KiserDesigns/Monorail/Plate DXFs/Cutouts Only/m0n0rail_steam.dxf

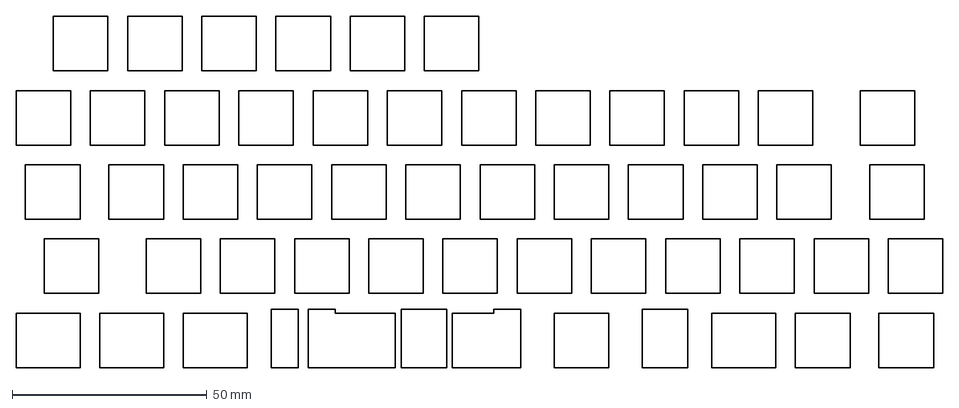
[picture p15: CAD file, 2022-03-02]
Plate DXFs/Cutouts Only/m0n0rail_steam.dxf
237.8 x 90.2 mm
