KiserDesigns/Monorail/Plate DXFs/Jet Hullagon.dxf

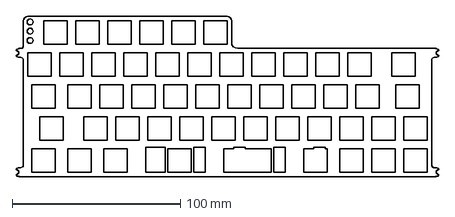
[picture p16: CAD file, 2022-03-02]
Plate DXFs/Jet Hullagon.dxf
251.3 x 95.2 mm
