KiserDesigns/Monorail/Plate DXFs/Cutouts Only/monorail_steam.dxf

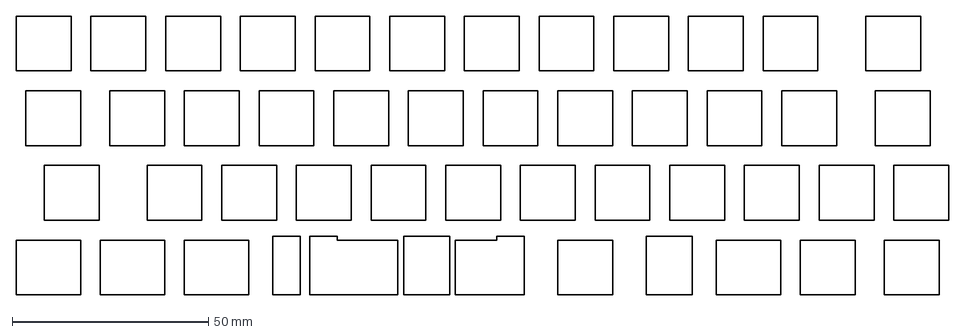
[picture p17: CAD file, 2022-03-02]
Plate DXFs/Cutouts Only/monorail_steam.dxf
237.8 x 71.1 mm
