KiserDesigns/Monorail/Plate DXFs/Diesel Vanagon.dxf

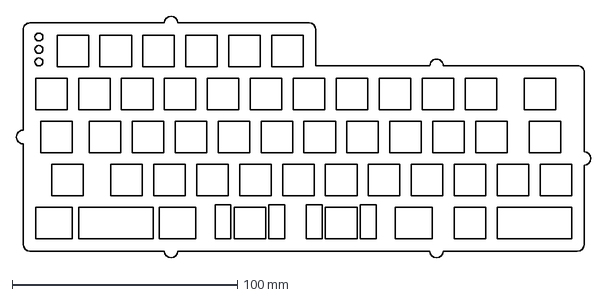
[picture p18: CAD file, 2022-03-02]
Plate DXFs/Diesel Vanagon.dxf
255.0 x 107.3 mm
