KiserDesigns/Monorail/Plate DXFs/Jet Coriander.dxf

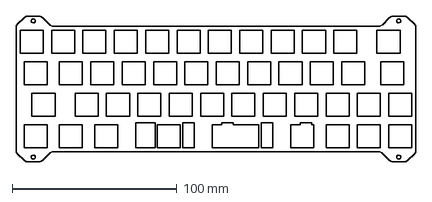
[picture p19: CAD file, 2022-03-02]
Plate DXFs/Jet Coriander.dxf
242.9 x 88.2 mm
