KiserDesigns/Monorail/Plate DXFs/Jet Tray Mount.dxf

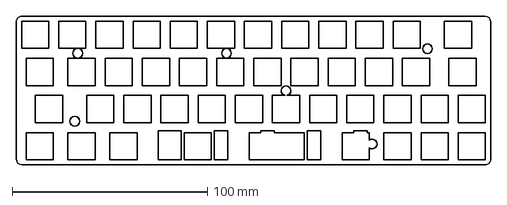
[picture p20: CAD file, 2022-03-02]
Plate DXFs/Jet Tray Mount.dxf
243.4 x 76.2 mm
