KiserDesigns/Monorail/Plate DXFs/Diesel Hull.dxf

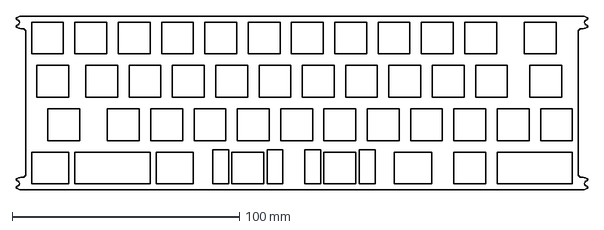
[picture p21: CAD file, 2022-03-02]
Plate DXFs/Diesel Hull.dxf
251.3 x 76.2 mm
