KiserDesigns/Monorail/Plate DXFs/Steam Coriander.dxf

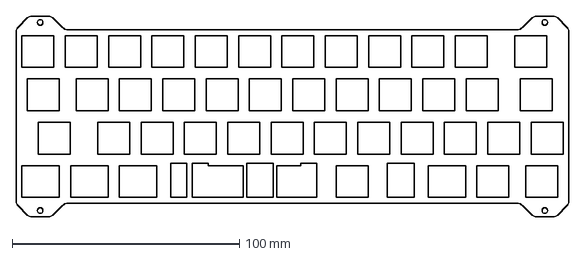
[picture p22: CAD file, 2022-03-02]
Plate DXFs/Steam Coriander.dxf
242.9 x 88.2 mm
