KiserDesigns/Monorail/Plate DXFs/Jet Hull.dxf

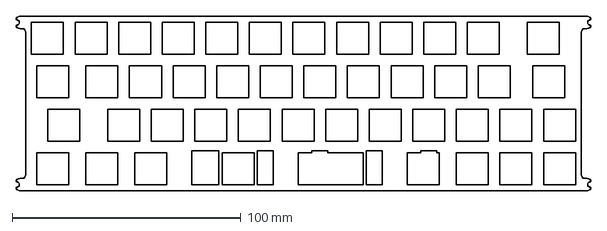
[picture p23: CAD file, 2022-03-02]
Plate DXFs/Jet Hull.dxf
251.3 x 76.2 mm
