KiserDesigns/Monorail/Plate DXFs/Combined Vanagon.dxf

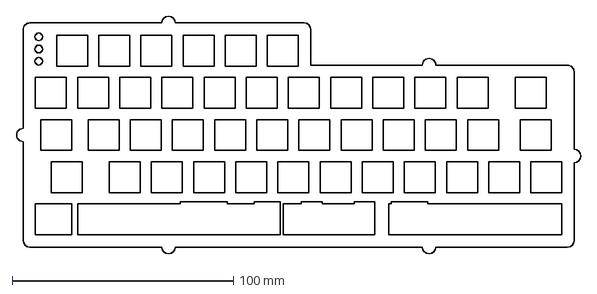
[picture p24: CAD file, 2022-03-02]
Plate DXFs/Combined Vanagon.dxf
255.0 x 107.3 mm
