KiserDesigns/Monorail/Plate DXFs/Steam Vanagon.dxf

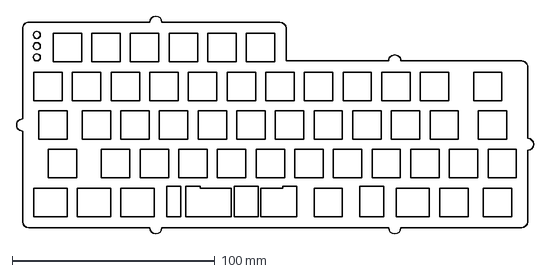
[picture p25: CAD file, 2022-03-02]
Plate DXFs/Steam Vanagon.dxf
255.0 x 107.3 mm
