KiserDesigns/Monorail/Plate DXFs/Combined Hullagon.dxf

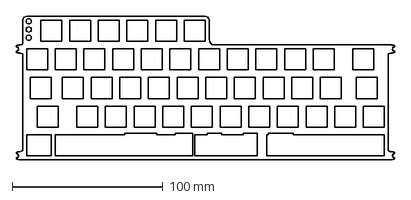
[picture p26: CAD file, 2022-03-02]
Plate DXFs/Combined Hullagon.dxf
251.3 x 95.2 mm
