KiserDesigns/Monorail/Plate DXFs/Combined Tray Mount.dxf

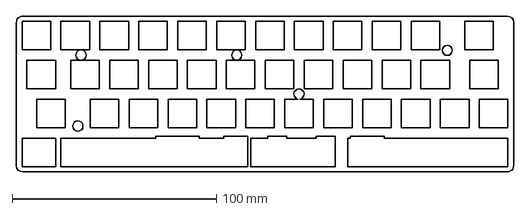
[picture p27: CAD file, 2022-03-02]
Plate DXFs/Combined Tray Mount.dxf
243.4 x 76.2 mm
