KiserDesigns/Monorail/Plate DXFs/Steam Hullagon.dxf

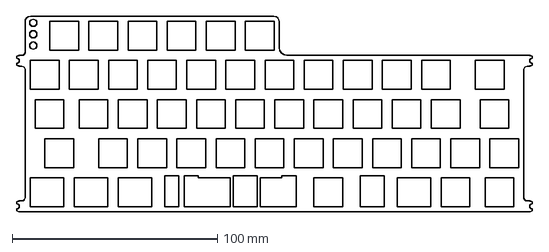
[picture p28: CAD file, 2022-03-02]
Plate DXFs/Steam Hullagon.dxf
251.3 x 95.2 mm
