KiserDesigns/Monorail/Plate DXFs/Steam Hull.dxf

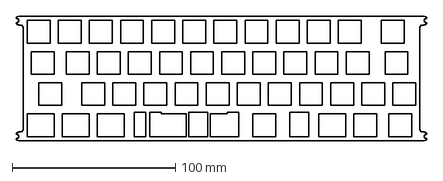
[picture p29: CAD file, 2022-03-02]
Plate DXFs/Steam Hull.dxf
251.3 x 76.2 mm
