KiserDesigns/Monorail/Plate DXFs/Steam Tray Mount.dxf

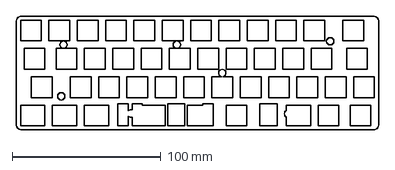
[picture p30: CAD file, 2022-03-02]
Plate DXFs/Steam Tray Mount.dxf
243.4 x 76.2 mm
