KiserDesigns/Monorail/PCB Sources/Monorail_Diesel_Reduced/Monorail_Diesel_Reduced.kicad_sch

## KiCad design PCB Sources/Monorail_Diesel_Reduced/Monorail_Diesel_Reduced.kicad_sch (2023-07-24)

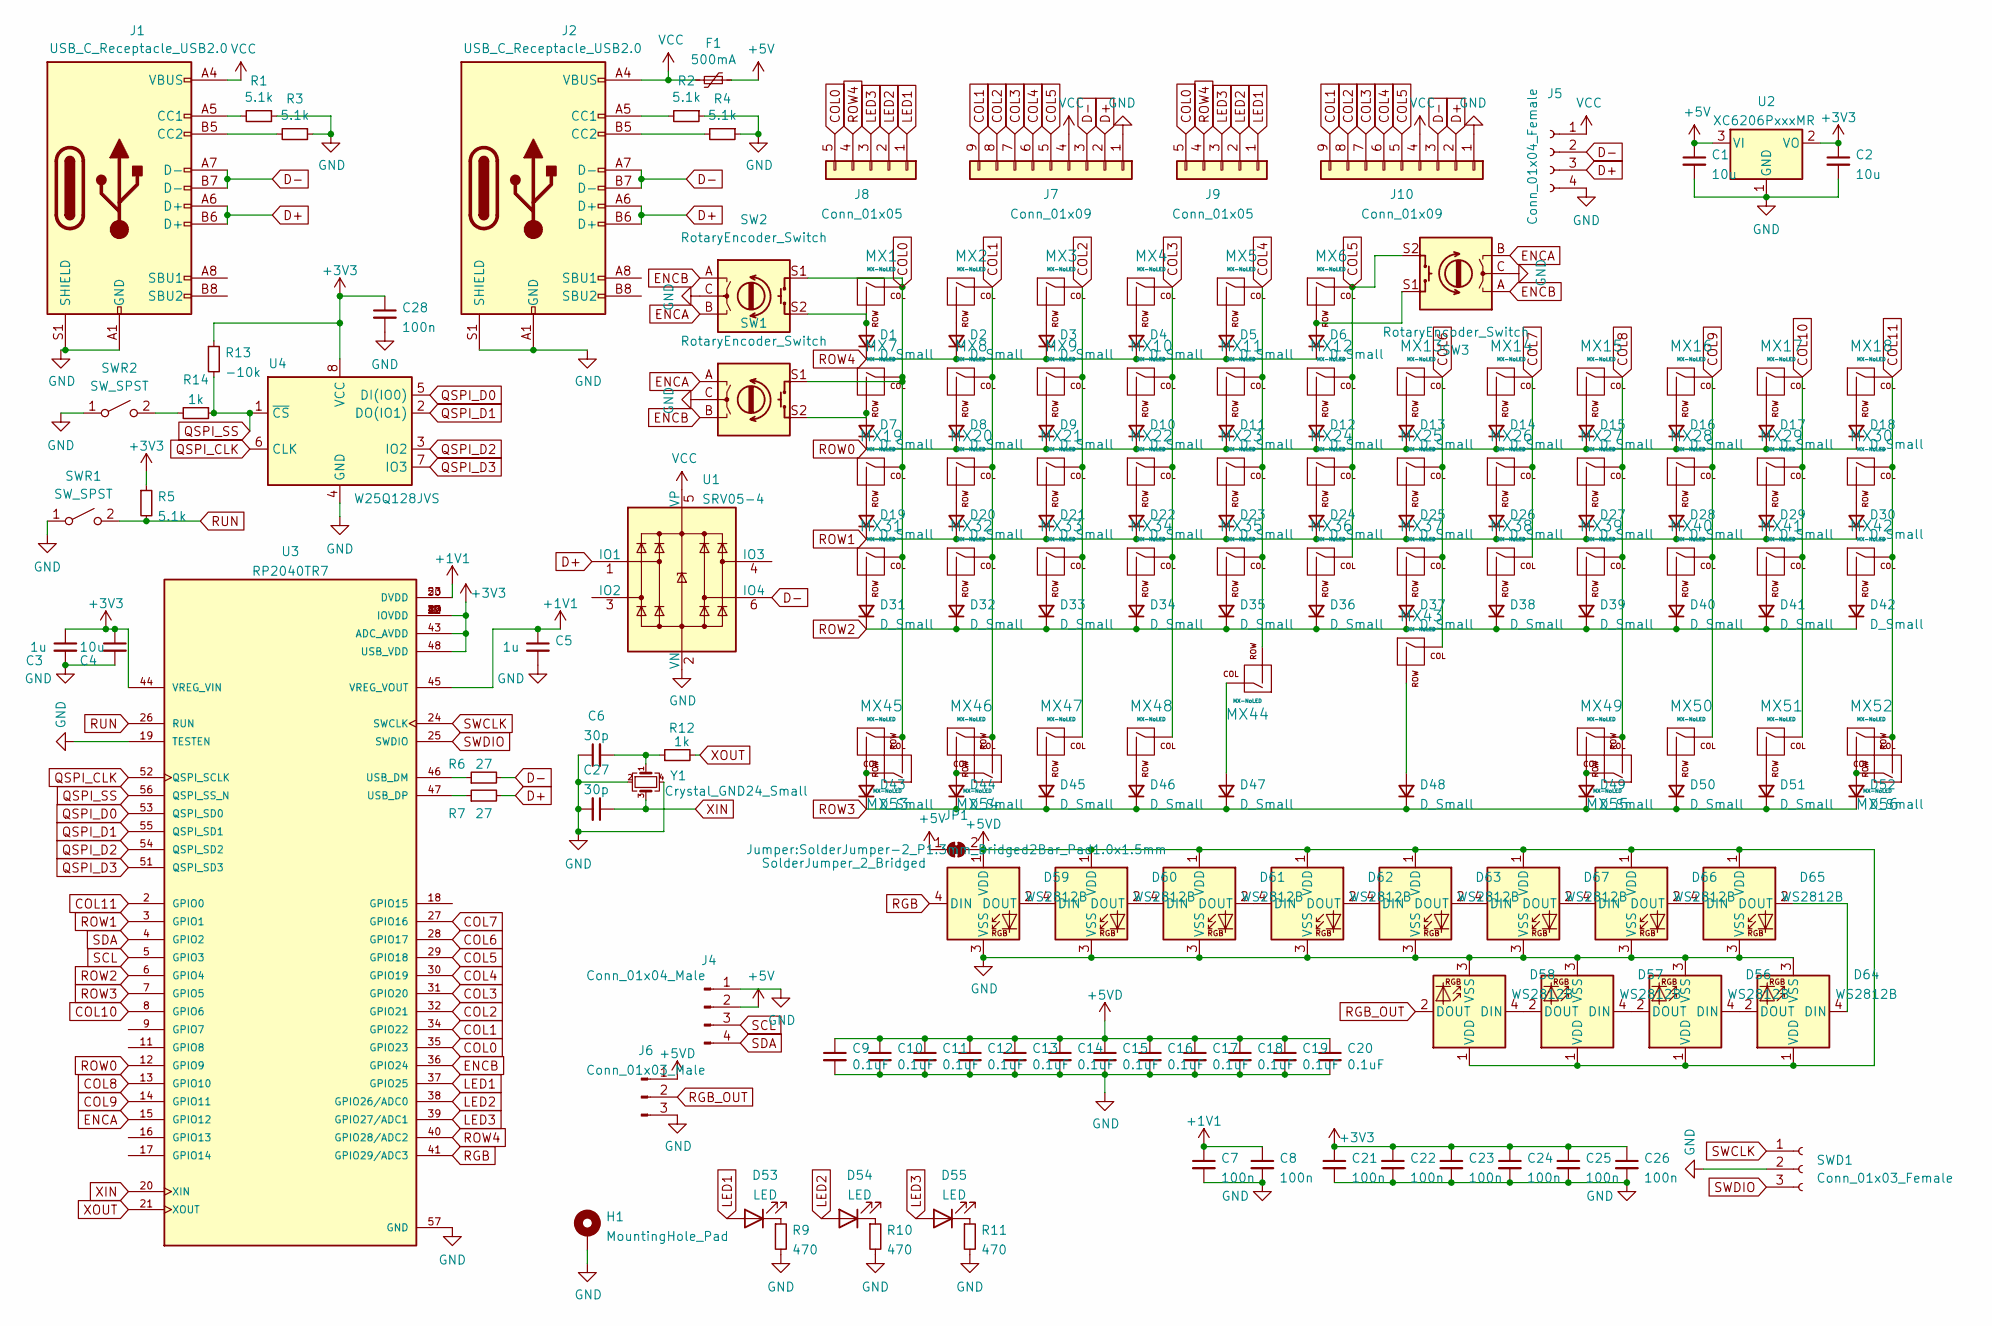
[picture p31: schematic Monorail_Diesel_Reduced.kicad_sch]

Parts:
C1, C2, C4: 10u; C_0402_1005Metric
C3, C5: 1u; C_0402_1005Metric
C6, C27: 30p; C_0402_1005Metric
C7, C8, C21, C22, C23, C24, C25, C26, C28: 100n; C_0402_1005Metric
C9, C10, C11, C12, C13, C14, C15, C16, C17, C18, C19, C20: 0.1uF; C_0603_1608Metric
D1, D2, D3, D4, D5, D6, D7, D8, D9, D10, D11, D12, D13, D14, D15, D16, D17, D18, D19, D20, D21, D22, D23, D24, D25, D26, D27, D28, D29, D30, D31, D32, D33, D34, D35, D36, D37, D38, D39, D40, D41, D42, D43, D44, D45, D46, D47, D48, D49, D50, D51, D52: D_Small; D_SOD-123
D53, D54, D55: LED; LED_D3.0mm
D56, D57, D58, D59, D60, D61, D62, D63, D64, D65, D66, D67: WS2812B; LED_WS2812B_2020
F1: 500mA; Fuse_1206_3216Metric
H1: MountingHole_Pad; Minivan-reference
J1, J2: USB_C_Receptacle_USB2.0; USB_C_Receptacle_HRO_TYPE-C-31-M-12
J4: Conn_01x04_Male; PinHeader_1x04_P2.54mm_Vertical
J5: Conn_01x04_Female; JST_SH_SM04B-SRSS-TB_1x04-1MP_P1.00mm_Horizontal
J6: Conn_01x03_Male; PinHeader_1x03_P2.54mm_Vertical
J7, J10: Conn_01x09; PinHeader_1x09_P2.54mm_Vertical
J8, J9: Conn_01x05; PinHeader_1x05_P2.54mm_Vertical
JP1: SolderJumper_2_Bridged; SolderJumper-2_P1.3mm_Bridged2Bar_Pad1.0x1.5mm
MX1, MX2, MX3, MX4, MX5, MX6, MX7, MX8, MX9, MX10, MX11, MX12, MX13, MX14, MX15, MX16, MX17, MX20, MX21, MX22, MX23, MX24, MX25, MX26, MX27, MX28, MX29, MX32, MX33, MX34, MX35, MX36, MX37, MX38, MX39, MX40, MX41, MX42, MX45, MX46, MX47, MX48, MX51, MX56: MX-NoLED; MXOnly-1U-Hotswap
MX18, MX31, MX52: MX-NoLED; MXOnly-1.75U-Hotswap
MX19, MX53, MX55: MX-NoLED; MXOnly-1.25U-Hotswap
MX30, MX49, MX50, MX54: MX-NoLED; MXOnly-1.5U-Hotswap
MX43: MX-NoLED; MXOnly-2U-Hotswap-ReversedStabilizers
MX44: MX-NoLED; MXOnly-2.25U-Hotswap-ReversedStabilizers
R1, R2, R3, R4: 5.1k; R_0603_1608Metric
R5: 5.1k; R_0402_1005Metric
R6, R7: 27; R_0402_1005Metric
R9, R10, R11: 470; R_0603_1608Metric
R12, R14: 1k; R_0402_1005Metric
R13: -10k; R_0603_1608Metric
SW1, SW2, SW3: RotaryEncoder_Switch; RotaryEncoder_Alps_EC11E-Switch_Vertical_H20mm
SWD1: Conn_01x03_Female; PinHeader_1x03_P2.54mm_Vertical
SWR1, SWR2: SW_SPST; SW_SPST_TL3342
U1: SRV05-4; SOT-23-6
U2: XC6206PxxxMR; SOT-23
U3: RP2040TR7; QFN40P700X700X90-57N; PARTREV 1.7.1
U4: W25Q128JVS; SOIC-8_5.23x5.23mm_P1.27mm
Y1: Crystal_GND24_Small; Crystal_SMD_3225-4Pin_3.2x2.5mm

Connections:
+1V1: C5.1, C7.1, C8.1, U3.23 (DVDD), U3.45 (VREG_VOUT), U3.50 (DVDD)
+3V3: C2.1, C3.1, C4.1, C21.1, C22.1, C23.1, C24.1, C25.1, C26.1, C28.1, R5.1, R13.1, U2.2 (VO), U3.1 (IOVDD), U3.10 (IOVDD), U3.22 (IOVDD), U3.33 (IOVDD), U3.42 (IOVDD), U3.43 (ADC_AVDD), U3.44 (VREG_VIN), U3.48 (USB_VDD), U3.49 (IOVDD), U4.8 (VCC)
+5V: C1.1, F1.1, J4.2, JP1.1 (A), U2.3 (VI)
+5VD: C9.1, C10.1, C11.1, C12.1, C13.1, C14.1, C15.1, C16.1, C17.1, C18.1, C19.1, C20.1, D56.1 (VDD), D57.1 (VDD), D58.1 (VDD), D59.1 (VDD), D60.1 (VDD), D61.1 (VDD), D62.1 (VDD), D63.1 (VDD), D64.1 (VDD), D65.1 (VDD), D66.1 (VDD), D67.1 (VDD), J6.1, JP1.2 (B)
COL0: J8.5, J9.5, MX1.1 (COL), MX7.1 (COL), MX19.1 (COL), MX31.1 (COL), MX45.1 (COL), MX53.2 (ROW), SW1.S1, SW2.S1, U3.35 (GPIO23)
COL1: J7.9, J10.9, MX2.1 (COL), MX8.1 (COL), MX20.1 (COL), MX32.1 (COL), MX46.1 (COL), MX54.2 (ROW), U3.34 (GPIO22)
COL2: J7.8, J10.8, MX3.1 (COL), MX9.1 (COL), MX21.1 (COL), MX33.1 (COL), MX47.1 (COL), U3.32 (GPIO21)
COL3: J7.7, J10.7, MX4.1 (COL), MX10.1 (COL), MX22.1 (COL), MX34.1 (COL), MX48.1 (COL), U3.31 (GPIO20)
COL4: J7.6, J10.6, MX5.1 (COL), MX11.1 (COL), MX23.1 (COL), MX35.1 (COL), MX44.2 (ROW), U3.30 (GPIO19)
COL5: J7.5, J10.5, MX6.1 (COL), MX12.1 (COL), MX24.1 (COL), MX36.1 (COL), SW3.S2, U3.29 (GPIO18)
COL6: MX13.1 (COL), MX25.1 (COL), MX37.1 (COL), MX43.1 (COL), U3.28 (GPIO17)
COL7: MX14.1 (COL), MX26.1 (COL), MX38.1 (COL), U3.27 (GPIO16)
COL8: MX15.1 (COL), MX27.1 (COL), MX39.1 (COL), MX49.1 (COL), MX55.2 (ROW), U3.13 (GPIO10)
COL9: MX16.1 (COL), MX28.1 (COL), MX40.1 (COL), MX50.1 (COL), U3.14 (GPIO11)
COL10: MX17.1 (COL), MX29.1 (COL), MX41.1 (COL), MX51.1 (COL), U3.8 (GPIO6)
COL11: MX18.1 (COL), MX30.1 (COL), MX42.1 (COL), MX52.1 (COL), MX56.2 (ROW), U3.2 (GPIO0)
D+: J1.A6 (D+), J1.B6 (D+), J2.A6 (D+), J2.B6 (D+), J5.3, J7.2, J10.2, R7.2, U1.1 (IO1)
D-: J1.A7 (D-), J1.B7 (D-), J2.A7 (D-), J2.B7 (D-), J5.2, J7.3, J10.3, R6.2, U1.6 (IO4)
ENCA: SW1.A, SW2.B, SW3.B, U3.15 (GPIO12)
ENCB: SW1.B, SW2.A, SW3.A, U3.36 (GPIO24)
GND: C1.2, C2.2, C3.2, C4.2, C5.2, C6.1, C7.2, C8.2, C9.2, C10.2, C11.2, C12.2, C13.2, C14.2, C15.2, C16.2, C17.2, C18.2, C19.2, C20.2, C21.2, C22.2, C23.2, C24.2, C25.2, C26.2, C27.2, C28.2, D56.3 (VSS), D57.3 (VSS), D58.3 (VSS), D59.3 (VSS), D60.3 (VSS), D61.3 (VSS), D62.3 (VSS), D63.3 (VSS), D64.3 (VSS), D65.3 (VSS), D66.3 (VSS), D67.3 (VSS), H1.1, J1.A1 (GND), J1.A12 (GND), J1.B1 (GND), J1.B12 (GND), J1.S1 (SHIELD), J2.A1 (GND), J2.A12 (GND), J2.B1 (GND), J2.B12 (GND), J2.S1 (SHIELD), J4.1, J5.4, J6.3, J7.1, J10.1, R1.1, R2.1, R3.1, R4.1, R9.2, R10.2, R11.2, SW1.C, SW2.C, SW3.C, SWD1.2, SWR1.1 (A), SWR2.1 (A), U1.2 (VN), U2.1 (GND), U3.19 (TESTEN), U3.57 (GND), U4.4 (GND), Y1.2, Y1.4
LED1: D53.2 (A), J8.1, J9.1, U3.37 (GPIO25)
LED2: D54.2 (A), J8.2, J9.2, U3.38 (GPIO26/ADC0)
LED3: D55.2 (A), J8.3, J9.3, U3.39 (GPIO27/ADC1)
unnamed: C6.2, R12.1, Y1.1
unnamed: D1.2 (A), MX1.2 (ROW), SW2.S2
unnamed: D2.2 (A), MX2.2 (ROW)
unnamed: D3.2 (A), MX3.2 (ROW)
unnamed: D4.2 (A), MX4.2 (ROW)
unnamed: D5.2 (A), MX5.2 (ROW)
unnamed: D6.2 (A), MX6.2 (ROW), SW3.S1
unnamed: D7.2 (A), MX7.2 (ROW), SW1.S2
unnamed: D8.2 (A), MX8.2 (ROW)
unnamed: D9.2 (A), MX9.2 (ROW)
unnamed: D10.2 (A), MX10.2 (ROW)
unnamed: D11.2 (A), MX11.2 (ROW)
unnamed: D12.2 (A), MX12.2 (ROW)
unnamed: D13.2 (A), MX13.2 (ROW)
unnamed: D14.2 (A), MX14.2 (ROW)
unnamed: D15.2 (A), MX15.2 (ROW)
unnamed: D16.2 (A), MX16.2 (ROW)
unnamed: D17.2 (A), MX17.2 (ROW)
unnamed: D18.2 (A), MX18.2 (ROW)
unnamed: D19.2 (A), MX19.2 (ROW)
unnamed: D20.2 (A), MX20.2 (ROW)
unnamed: D21.2 (A), MX21.2 (ROW)
unnamed: D22.2 (A), MX22.2 (ROW)
unnamed: D23.2 (A), MX23.2 (ROW)
unnamed: D24.2 (A), MX24.2 (ROW)
unnamed: D25.2 (A), MX25.2 (ROW)
unnamed: D26.2 (A), MX26.2 (ROW)
unnamed: D27.2 (A), MX27.2 (ROW)
unnamed: D28.2 (A), MX28.2 (ROW)
unnamed: D29.2 (A), MX29.2 (ROW)
unnamed: D30.2 (A), MX30.2 (ROW)
unnamed: D31.2 (A), MX31.2 (ROW)
unnamed: D32.2 (A), MX32.2 (ROW)
unnamed: D33.2 (A), MX33.2 (ROW)
unnamed: D34.2 (A), MX34.2 (ROW)
unnamed: D35.2 (A), MX35.2 (ROW)
unnamed: D36.2 (A), MX36.2 (ROW)
unnamed: D37.2 (A), MX37.2 (ROW)
unnamed: D38.2 (A), MX38.2 (ROW)
unnamed: D39.2 (A), MX39.2 (ROW)
unnamed: D40.2 (A), MX40.2 (ROW)
unnamed: D41.2 (A), MX41.2 (ROW)
unnamed: D42.2 (A), MX42.2 (ROW)
unnamed: D43.2 (A), MX45.2 (ROW), MX53.1 (COL)
unnamed: D44.2 (A), MX46.2 (ROW), MX54.1 (COL)
unnamed: D45.2 (A), MX47.2 (ROW)
unnamed: D46.2 (A), MX48.2 (ROW)
unnamed: D47.2 (A), MX44.1 (COL)
unnamed: D48.2 (A), MX43.2 (ROW)
unnamed: D49.2 (A), MX49.2 (ROW), MX55.1 (COL)
unnamed: D50.2 (A), MX50.2 (ROW)
unnamed: D51.2 (A), MX51.2 (ROW)
unnamed: D52.2 (A), MX52.2 (ROW), MX56.1 (COL)
unnamed: D53.1 (K), R9.1
unnamed: D54.1 (K), R10.1
unnamed: D55.1 (K), R11.1
unnamed: D56.2 (DOUT), D57.4 (DIN)
unnamed: D56.4 (DIN), D64.2 (DOUT)
unnamed: D57.2 (DOUT), D58.4 (DIN)
unnamed: D59.2 (DOUT), D60.4 (DIN)
unnamed: D60.2 (DOUT), D61.4 (DIN)
unnamed: D61.2 (DOUT), D62.4 (DIN)
unnamed: D62.2 (DOUT), D63.4 (DIN)
unnamed: D63.2 (DOUT), D67.4 (DIN)
unnamed: D64.4 (DIN), D65.2 (DOUT)
unnamed: D65.4 (DIN), D66.2 (DOUT)
unnamed: D66.4 (DIN), D67.2 (DOUT)
unnamed: J1.A5 (CC1), R1.2
unnamed: J1.B5 (CC2), R3.2
unnamed: J2.A5 (CC1), R2.2
unnamed: J2.B5 (CC2), R4.2
unnamed: R6.1, U3.46 (USB_DM)
unnamed: R7.1, U3.47 (USB_DP)
unnamed: R14.2, SWR2.2 (B)
QSPI_CLK: U3.52 (QSPI_SCLK), U4.6 (CLK)
QSPI_D0: U3.53 (QSPI_SD0), U4.5 (DI(IO0))
QSPI_D1: U3.55 (QSPI_SD1), U4.2 (DO(IO1))
QSPI_D2: U3.54 (QSPI_SD2), U4.3 (IO2)
QSPI_D3: U3.51 (QSPI_SD3), U4.7 (IO3)
QSPI_SS: R13.2, R14.1, U3.56 (QSPI_SS_N), U4.1 (~CS)
RGB: D59.4 (DIN), U3.41 (GPIO29/ADC3)
RGB_OUT: D58.2 (DOUT), J6.2
ROW0: D7.1 (K), D8.1 (K), D9.1 (K), D10.1 (K), D11.1 (K), D12.1 (K), D13.1 (K), D14.1 (K), D15.1 (K), D16.1 (K), D17.1 (K), D18.1 (K), U3.12 (GPIO9)
ROW1: D19.1 (K), D20.1 (K), D21.1 (K), D22.1 (K), D23.1 (K), D24.1 (K), D25.1 (K), D26.1 (K), D27.1 (K), D28.1 (K), D29.1 (K), D30.1 (K), U3.3 (GPIO1)
ROW2: D31.1 (K), D32.1 (K), D33.1 (K), D34.1 (K), D35.1 (K), D36.1 (K), D37.1 (K), D38.1 (K), D39.1 (K), D40.1 (K), D41.1 (K), D42.1 (K), U3.6 (GPIO4)
ROW3: D43.1 (K), D44.1 (K), D45.1 (K), D46.1 (K), D47.1 (K), D48.1 (K), D49.1 (K), D50.1 (K), D51.1 (K), D52.1 (K), U3.7 (GPIO5)
ROW4: D1.1 (K), D2.1 (K), D3.1 (K), D4.1 (K), D5.1 (K), D6.1 (K), J8.4, J9.4, U3.40 (GPIO28/ADC2)
RUN: R5.2, SWR1.2 (B), U3.26 (RUN)
SCL: J4.3, U3.5 (GPIO3)
SDA: J4.4, U3.4 (GPIO2)
SWCLK: SWD1.1, U3.24 (SWCLK)
SWDIO: SWD1.3, U3.25 (SWDIO)
VCC: F1.2, J1.A4 (VBUS), J1.A9 (VBUS), J1.B4 (VBUS), J1.B9 (VBUS), J2.A4 (VBUS), J2.A9 (VBUS), J2.B4 (VBUS), J2.B9 (VBUS), J5.1, J7.4, J10.4, U1.5 (VP)
XIN: C27.1, U3.20 (XIN), Y1.3
XOUT: R12.2, U3.21 (XOUT)
